paulbardini/Assistive-Joystick/img/Modifications/Image00001 smaller.jpg

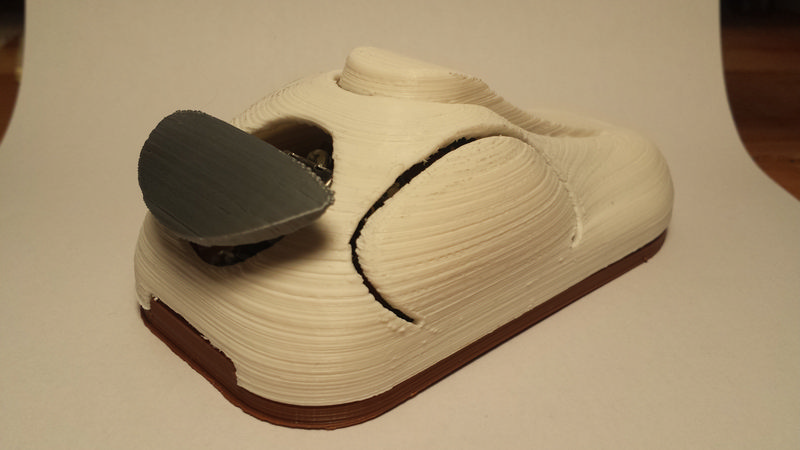
img/Modifications/Image00001 smaller.jpg
