paulbardini/Assistive-Joystick/img/Research/Image00004 smaller.jpg

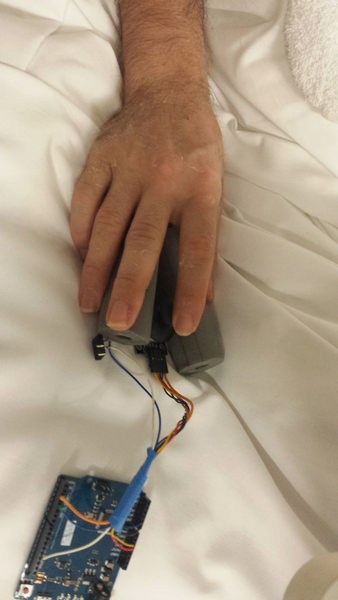
img/Research/Image00004 smaller.jpg
