paulbardini/Assistive-Joystick/img/Research/Image00005 smaller.jpg

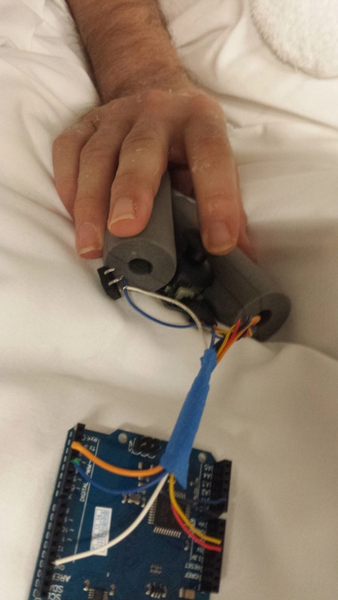
img/Research/Image00005 smaller.jpg
