paulbardini/Assistive-Joystick/img/Making/Image00017 smaller.jpg

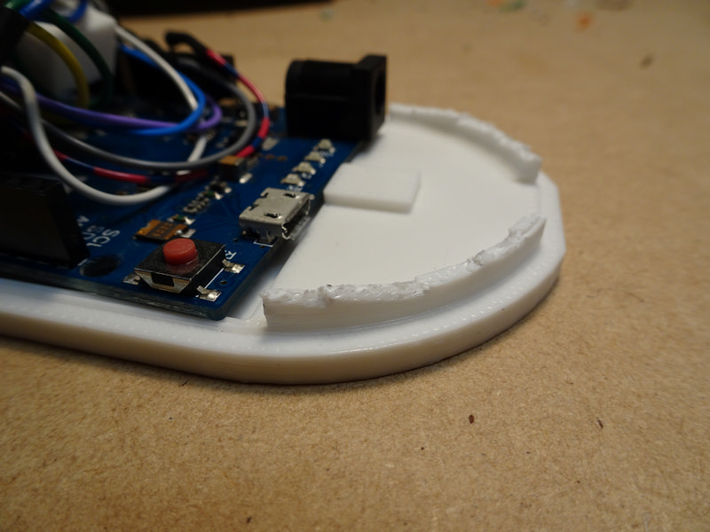
img/Making/Image00017 smaller.jpg
